gdoor-org/gdoor/firmware/esp32/gdoor/src/gdoor_tx.cpp

/* 
 * This file is part of the GDoor distribution (https://github.com/gdoor-org).
 * Copyright (c) 2024 GDoor authors.
 * 
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
 * You should have received a copy of the GNU General Public License 
 * along with this program. If not, see <http://www.gnu.org/licenses/>.
 */
#include "defines.h"
#include "gdoor_tx.h"
#include "gdoor_rx.h"
#include "gdoor_utils.h"

namespace GDOOR_TX {
    uint16_t tx_state = 0;
    uint16_t tx_words[MAX_WORDLEN];
    uint8_t tx_strbuffer[MAX_WORDLEN*2];
    uint16_t bits_len = 0;
    uint16_t bits_ptr = 0;
    uint16_t pulse_cnt = 0;
    uint8_t startbit_send = 0;

    uint8_t timer_oc_state = 0;

    uint8_t pin_tx = 0;
    uint8_t pin_tx_en = 0;

    hw_timer_t* timer_60khz = NULL;
    const String hexChars =  F("0123456789ABCDEF");

    static inline uint16_t bit2pulselen(uint16_t bit) {
        if (bit) {
            return ONE_PULSENUM;
        } else {
            return ZERO_PULSENUM;
        }
    }

    static inline uint16_t extractBitLen(uint16_t word, uint8_t bitindex) {
        return bit2pulselen((uint16_t) (word & (uint16_t)(0x01<<bitindex))); //LSB first
    }

    static inline uint16_t byte2word(uint8_t byte) {
        uint16_t value = byte & 0x00FF;
        if(GDOOR_UTILS::parity_odd(byte)) { //If parity, set MSB
            value |= 0x100;
        }
        return value;
    }

    static inline void start_timer() {
        tx_state |= STATE_SENDING;
        bits_ptr = 0;
        pulse_cnt = 0;
        timer_oc_state = 0;
        startbit_send = 0;

        //Workaround: Disable comparator to not be disturbed by receive.
        //Better sending scheme is needed
        GDOOR_RX::disable();

        //TX Enable Pin high
        digitalWrite(pin_tx_en, HIGH);

        timerStart(timer_60khz); //Start timer 2 to send out bitstream
    }

    static inline void stop_timer() {
        //timer_set_outputcompare(&htim2, 0);
        bits_ptr = 0;
        pulse_cnt = 0;
        startbit_send = 0;

        // PWM off
        ledcWrite(pin_tx, 0);

        //TX Enable Pin Low
        digitalWrite(pin_tx_en, LOW);
        timerStop(timer_60khz);
        tx_state &= (uint16_t)~STATE_SENDING;
        //Workaround: Enable comparator after sending
        //Better sending scheme is needed
        GDOOR_RX::enable();
    }


    /*
    * This is the sending timer interrupt
    */
    void isr_timer_60khz() {
        if(pulse_cnt == 0) { // Update timer, we send out (or waited) enough timer ticks to go to next bit
            if (bits_ptr >= bits_len || bits_ptr >= MAX_WORDLEN*9) {//We send everything
                stop_timer();
                return;
            }

            if(timer_oc_state == 1) {
                // Do not send next 60khz pulses, but send pause (nothing)
                timer_oc_state = 0;
                pulse_cnt = PAUSE_PULSENUM;
                ledcWrite(pin_tx, 0); //disable timer pulse output to send pause
            } else {
                // Load new tick values
                if (!startbit_send) { //First bit, is start bit with fixed value
                    pulse_cnt = STARTBIT_PULSENUM;
                    startbit_send = 1;
                } else { //Startbit was send, so load bit values now
                    uint8_t wordindex = (uint8_t) bits_ptr/9;
                    uint8_t bitindex = (uint8_t) bits_ptr%9;
                    uint16_t word = tx_words[wordindex];

                    pulse_cnt = extractBitLen(word, bitindex);
                    bits_ptr = bits_ptr + 1;
                }

                timer_oc_state = 1; //Signal that we are sending, so next time a pause will happen
                ledcWrite(pin_tx, 127); //Enable timer pulse output to send pulses forming the bit
            }
        } else { // Just update timer ticks, we are not finished yet
            pulse_cnt = pulse_cnt - 1;
        }
    }

    /*
    * Function called by user to setup everything needed for GDoor.
    * @param int txpin Pin number where PWM is created when sending out data
    * @param int txenpin Pin number where output buffer is turned on/off
    */
    void setup(uint8_t txpin, uint8_t txenpin) {
        pin_tx = txpin;
        pin_tx_en = txenpin;

        // Set timer_60khz timer frequency to 60kHz
        timer_60khz = timerBegin(60000);
        timerStop(timer_60khz);

        // Attach isr_timer_60khz function to timer_60khz timer.
        timerAttachInterrupt(timer_60khz, &isr_timer_60khz);

        // Set alarm to call isr_timer_60khz function
        // after 1 60kHz Cycles
        timerAlarm(timer_60khz, 1, true, 0);
        
        pinMode(pin_tx, OUTPUT);
        pinMode(pin_tx_en, OUTPUT);

        digitalWrite(pin_tx_en, LOW);
        digitalWrite(pin_tx, LOW);

        //Setup PWM subsystem (LEDC) on pin_tx
        // We only modulate with 52kHz, as the bandpass
        // manufacturing tolerances are a bit on the lower side.
        // Still works.
        ledcAttach(pin_tx, 52000, 8);
        ledcWrite(pin_tx, 0);

        stop_timer();
        bits_len = 0;
        tx_state = 0;
    }

    /*
    * Function called by user to send out data.
    * @param data buffer with bus data
    * @param len length of buffer, can be max MAX_WORDLEN
    */
    void send(uint8_t *data, uint16_t len) {
        if (! (tx_state & STATE_SENDING) && len < MAX_WORDLEN) {
            bits_ptr = 0;
            pulse_cnt = 0;
            bits_len = (uint16_t) (len*9 + 9); // Data bits + CRC (8bit CRC data + parity bit) (Startbit is added by timer int. routine)


            for (uint16_t i=0; i<len; i++) {
                uint8_t byte = data[i];
                tx_words[i] = byte2word(byte);
            }

            uint8_t crc = GDOOR_UTILS::crc(data, len);
            tx_words[len] = byte2word(crc);
            start_timer();
        }
    }

    /*
    * Function called by user to send out data.
    * @param hex string data without 0x prefix
    */
    void send(String str) {
        uint16_t index = 0;
        // String cleanup
        str.toUpperCase();

        // Only if we have enough memory
        if(str != "" && str.length() < MAX_WORDLEN*2) {
            // Convert from hex string to raw buffer array
            for(uint16_t i=0; i<str.length(); i+=2) {
                if(i < str.length()-1) { //To make sure that i+1 will not lead to overflow
                    int high = hexChars.indexOf(str[i]);
                    int low = hexChars.indexOf(str[i+1]);
                    if (high >= 0 && low >= 0) { // Check if input can be decoded as 8 bit hex value
                        tx_strbuffer[index] = high << 4 | low;
                        index++;
                    } else { // Abort on parse error
                        index = 0;
                        break;
                    }
                }
            }

            // If something was converted, transmit it
            if (index > 0) {
                send(tx_strbuffer, index);
            }
        }
    }
}
