gdoor-org/gdoor/firmware/esp32/gdoor/src/gdoor_rx.cpp

/* 
 * This file is part of the GDoor distribution (https://github.com/gdoor-org).
 * Copyright (c) 2024 GDoor authors.
 * 
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
 * You should have received a copy of the GNU General Public License 
 * along with this program. If not, see <http://www.gnu.org/licenses/>.
 */
#include "defines.h"
#include "gdoor_rx.h"
#include "gdoor_data.h"
#include "gdoor_utils.h"
#include "printer_helper.h"

namespace GDOOR_RX {

    uint16_t counts[MAX_WORDLEN*9]; // Received counter values of bitstream, buffer
    uint16_t isr_cnt = 0; // Interrupt Counter (Counting RX edges)  

    uint8_t words[MAX_WORDLEN]; //Received words buffer
    uint16_t raw[MAX_WORDLEN*9]; // Received raw counter values of bitstream

    uint16_t rx_state = 0; // State Machine

    uint8_t bitcounter = 0; //Current bit index, in currently active bitstream

    GDOOR_DATA retval;

    hw_timer_t * timer_bit_received = NULL;
    hw_timer_t * timer_bitstream_received = NULL;

    uint8_t pin_rx = 0;
    
    /*
    * We received a 60kHz pulse, so start timeout timer (for bit and whole bitstream) and increment bit pulse count,
    * so that logic knows how much pulses were in this bit pulse-train.
    */
    void ARDUINO_ISR_ATTR isr_extint_rx() {
        rx_state |= (uint16_t)FLAG_RX_ACTIVE;
        isr_cnt = isr_cnt + 1;
        timerWrite(timer_bit_received, 0); //reset timer
        timerWrite(timer_bitstream_received, 0); //reset timer
        timerStart(timer_bit_received); //Start timer to detect bit is over
        timerStart(timer_bitstream_received); //Start timer to detect bistream is over
    }

    /*
    * If this timer fires, the rx 60kHz pulse-train stopped,
    * so we should read out how many pulses we got for this bit (to decide 1 or 0)
    */
    void ARDUINO_ISR_ATTR isr_timer_bit_received() {
        if (bitcounter > MAX_WORDLEN*9) {
            bitcounter = 0;
        }
        counts[bitcounter] = isr_cnt;
        
        isr_cnt = 0;
        bitcounter = bitcounter + 1;
        timerStop(timer_bit_received);
    }

    /*
    * If this timer fires, rx bit stream is over
    */
    void ARDUINO_ISR_ATTR isr_timer_bitstream_received() {
        rx_state &= (uint16_t)~FLAG_RX_ACTIVE;
        rx_state |= (uint16_t)FLAG_BITSTREAM_RECEIVED;
        timerStop(timer_bitstream_received);
        timerStop(timer_bit_received);
    }

    /*
    * Internal function set reset all internal values.
    */
    void reset() {
        bitcounter = 0;
        isr_cnt = 0;
    }

    /*
    * Function to enable/disable RX, so that during TX we can disable RX to not get our own message
    */
    void enable() {
        reset();
        attachInterrupt(pin_rx, isr_extint_rx, FALLING);
    }

     /*
    * Function to enable/disable RX, so that during TX we can disable RX to not get our own message
    */
    void disable() {
        reset();
        detachInterrupt(pin_rx);
    }
    

    /*
    * Function called by user to setup everything needed for GDoor.
    * @param int rxpin Pin number where pulses from bus are received
    */
    void setup(uint8_t rxpin) {
        reset();
        pin_rx = rxpin;
        pinMode(pin_rx, INPUT);

        retval.len = 0;
        retval.valid = 0;

        // Set bit_received timer frequency to 120kHz
        timer_bit_received = timerBegin(120000);

        // Attach isr_timer_bit_received function to bit_received timer.
        timerAttachInterrupt(timer_bit_received, &isr_timer_bit_received);

        // Set alarm to call isr_timer_bit_received function
        // after 20 120kHz Cycles (=10 60kHz Cycles)
        timerAlarm(timer_bit_received, 20, true, 0);

        // Set bit_received timer frequency to 120kHz
        timer_bitstream_received = timerBegin(120000);

        // Attach isr_timer_bit_received function to bit_received timer.
        timerAttachInterrupt(timer_bitstream_received, &isr_timer_bitstream_received);

        // Set alarm to call isr_timer_bit_received function
        // after 6*STARTBIT_MIN_LEN 120kHz Cycles (= 3 * STARTBIT_MIN_LEN 60kHz Cycles)
        timerAlarm(timer_bitstream_received, 6*STARTBIT_MIN_LEN, true, 0);

        // Enable External RX Interrupt
        enable();

        // Set Timers to default values, just to be sure
        timerWrite(timer_bit_received, 0); //reset timer
        timerWrite(timer_bitstream_received, 0); //reset timer
        timerStop(timer_bitstream_received);
        timerStop(timer_bit_received);
    }

    /*
    * Function called by user, in main loop.
    * Needed for the decoding logic.
    */
    void loop() {
        if (rx_state & FLAG_BITSTREAM_RECEIVED) {
            rx_state &= (uint16_t)~FLAG_BITSTREAM_RECEIVED;
            JSONDEBUG("Gira RX done");
            if (retval.parse(counts, bitcounter)) {
                JSONDEBUG("Gira RX was successfully parsed");
                rx_state |= FLAG_DATA_READY;
            }
            reset();
        }
    }

    /**
    * User function, called to see if new data is available.
    * @return Data pointer as GDOOR_RX_DATA class or NULL if no data is available
    */
    GDOOR_DATA* read() {
        if(rx_state & FLAG_DATA_READY) {
            rx_state &= (uint16_t)~FLAG_DATA_READY;
            return &retval;
        }
        return NULL;
    }
}
